Sash-Reek2010/The-Mech/PCB/KiCAD/KEEB.kicad_sch

## KiCad design PCB/KiCAD/KEEB.kicad_sch (2026-04-22)

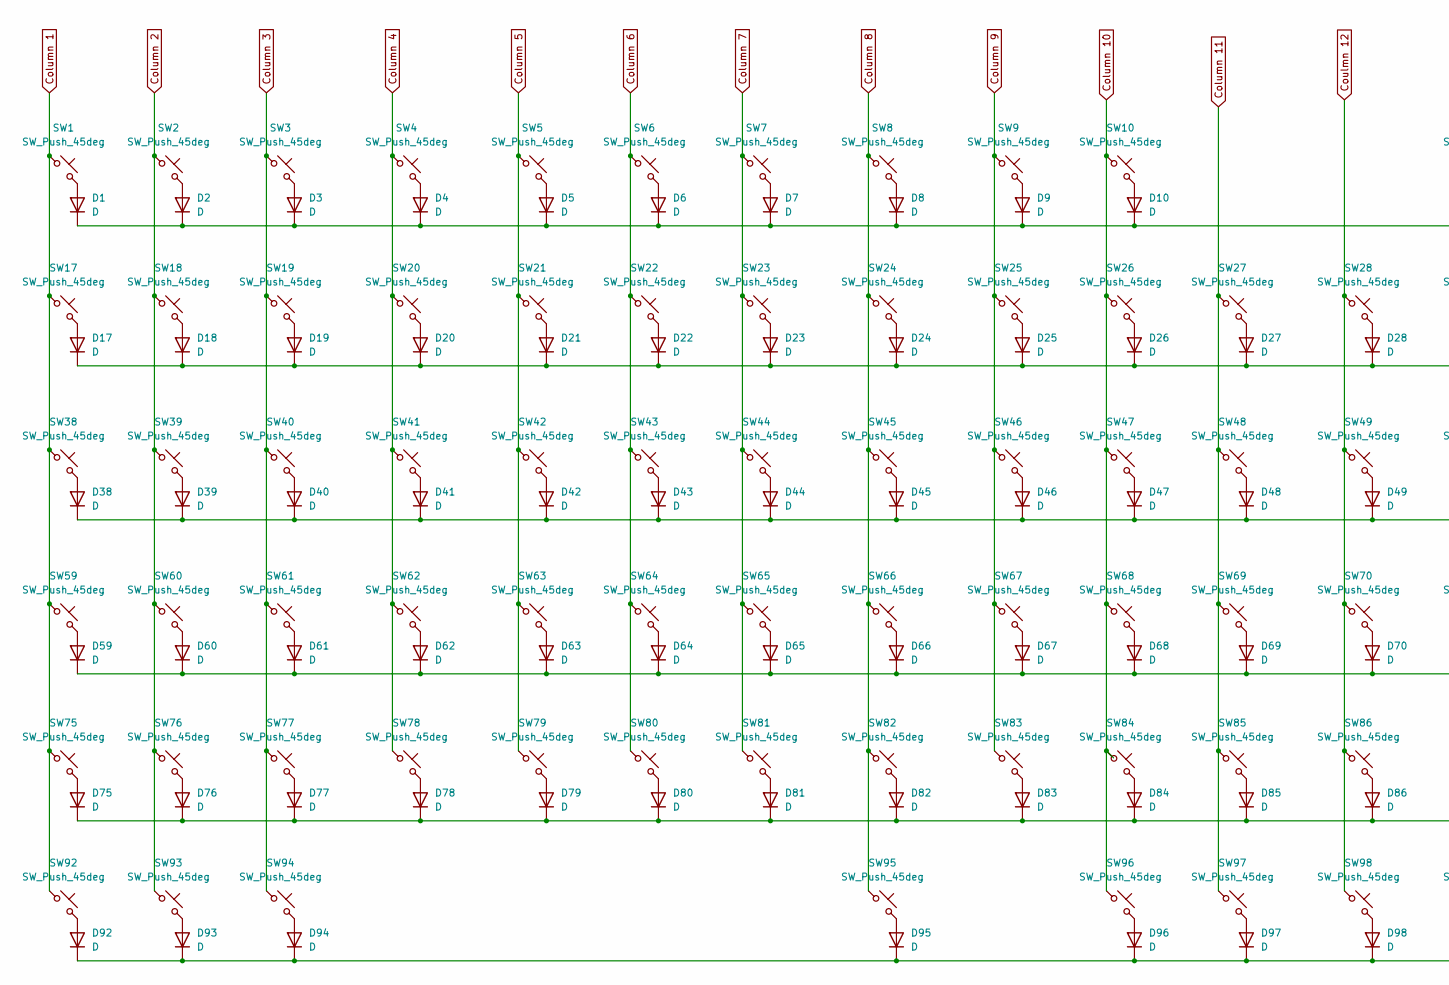
[picture p3: schematic KEEB.kicad_sch, part in row 1, column 1]

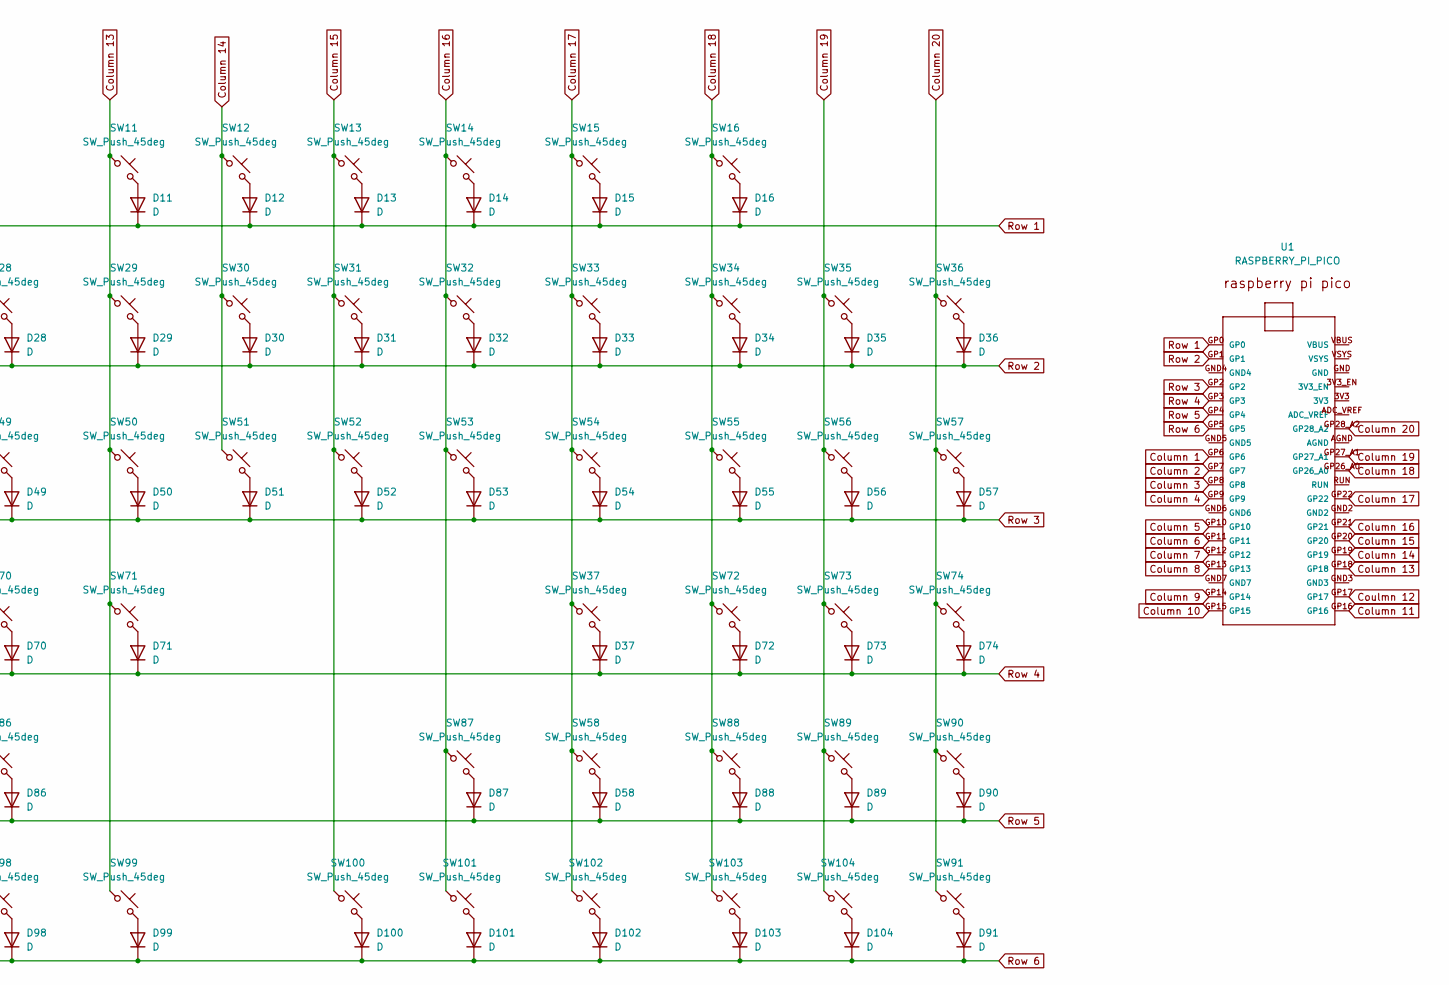
[picture p4: schematic KEEB.kicad_sch, part in row 1, column 2]

Parts:
D1, D2, D3, D4, D5, D6, D7, D8, D9, D10, D11, D12, D13, D14, D15, D16, D17, D18, D19, D20, D21, D22, D23, D24, D25, D26, D27, D28, D29, D30, D31, D32, D33, D34, D35, D36, D37, D38, D39, D40, D41, D42, D43, D44, D45, D46, D47, D48, D49, D50, D51, D52, D53, D54, D55, D56, D57, D58, D59, D60, D61, D62, D63, D64, D65, D66, D67, D68, D69, D70, D71, D72, D73, D74, D75, D76, D77, D78, D79, D80, D81, D82, D83, D84, D85, D86, D87, D88, D89, D90, D91, D92, D93, D94, D95, D96, D97, D98, D99, D100, D101, D102, D103, D104: D; Diode_DO-35
SW1, SW2, SW3, SW4, SW5, SW6, SW7, SW8, SW9, SW10, SW11, SW12, SW13, SW14, SW15, SW16, SW17, SW18, SW19, SW20, SW21, SW22, SW23, SW24, SW25, SW26, SW27, SW28, SW29, SW31, SW32, SW33, SW34, SW35, SW36, SW37, SW39, SW40, SW41, SW42, SW43, SW44, SW45, SW46, SW47, SW48, SW49, SW50, SW52, SW53, SW54, SW55, SW56, SW57, SW60, SW61, SW62, SW63, SW64, SW65, SW66, SW67, SW68, SW69, SW70, SW72, SW73, SW74, SW76, SW77, SW78, SW79, SW80, SW81, SW82, SW83, SW84, SW85, SW87, SW88, SW89, SW90, SW100, SW101, SW102, SW104: SW_Push_45deg; MX_PCB_1.00u
SW30, SW103: SW_Push_45deg; CherryMX_2.00u_StabWireTop
SW38, SW51: SW_Push_45deg; MX_PCB_1.50u
SW58, SW91: SW_Push_45deg; CherryMX_2.00u_PCB_StabWireTop TRUE ROTATED
SW59: SW_Push_45deg; MX_PCB_1.75u
SW71, SW75: SW_Push_45deg; CherryMX_2.25u_StabWireTop
SW86: SW_Push_45deg; CherryMX_2.75u_StabWireTop
SW92, SW93, SW94, SW96, SW97, SW98, SW99: SW_Push_45deg; MX_PCB_1.25u
SW95: SW_Push_45deg; CherryMX_6.25u_StabWireTop
U1: RASPBERRY_PI_PICO

Connections:
Column 1: SW1.1, SW17.1, SW38.1, SW59.1, SW75.1, SW92.1, U1.GP6
Column 2: SW2.1, SW18.1, SW39.1, SW60.1, SW76.1, SW93.1, U1.GP7
Column 3: SW3.1, SW19.1, SW40.1, SW61.1, SW77.1, SW94.1, U1.GP8
Column 4: SW4.1, SW20.1, SW41.1, SW62.1, SW78.1, U1.GP9
Column 5: SW5.1, SW21.1, SW42.1, SW63.1, SW79.1, U1.GP10
Column 6: SW6.1, SW22.1, SW43.1, SW64.1, SW80.1, U1.GP11
Column 7: SW7.1, SW23.1, SW44.1, SW65.1, SW81.1, U1.GP12
Column 8: SW8.1, SW24.1, SW45.1, SW66.1, SW82.1, SW95.1, U1.GP13
Column 9: SW9.1, SW25.1, SW46.1, SW67.1, SW83.1, U1.GP14
Column 10: SW10.1, SW26.1, SW47.1, SW68.1, SW84.1, SW96.1, U1.GP15
Column 11: SW27.1, SW48.1, SW69.1, SW85.1, SW97.1, U1.GP16
Column 13: SW11.1, SW29.1, SW50.1, SW71.1, SW99.1, U1.GP18
Column 14: SW12.1, SW30.1, SW51.1, U1.GP19
Column 15: SW13.1, SW31.1, SW52.1, SW100.1, U1.GP20
Column 16: SW14.1, SW32.1, SW53.1, SW87.1, SW101.1, U1.GP21
Column 17: SW15.1, SW33.1, SW37.1, SW54.1, SW58.1, SW102.1, U1.GP22
Column 18: SW16.1, SW34.1, SW55.1, SW72.1, SW88.1, SW103.1, U1.GP26_A0
Column 19: SW35.1, SW56.1, SW73.1, SW89.1, SW104.1, U1.GP27_A1
Column 20: SW36.1, SW57.1, SW74.1, SW90.1, SW91.1, U1.GP28_A2
Coulmn 12: SW28.1, SW49.1, SW70.1, SW86.1, SW98.1, U1.GP17
unnamed: D1.2 (A), SW1.2
unnamed: D2.2 (A), SW2.2
unnamed: D3.2 (A), SW3.2
unnamed: D4.2 (A), SW4.2
unnamed: D5.2 (A), SW5.2
unnamed: D6.2 (A), SW6.2
unnamed: D7.2 (A), SW7.2
unnamed: D8.2 (A), SW8.2
unnamed: D9.2 (A), SW9.2
unnamed: D10.2 (A), SW10.2
unnamed: D11.2 (A), SW11.2
unnamed: D12.2 (A), SW12.2
unnamed: D13.2 (A), SW13.2
unnamed: D14.2 (A), SW14.2
unnamed: D15.2 (A), SW15.2
unnamed: D16.2 (A), SW16.2
unnamed: D17.2 (A), SW17.2
unnamed: D18.2 (A), SW18.2
unnamed: D19.2 (A), SW19.2
unnamed: D20.2 (A), SW20.2
unnamed: D21.2 (A), SW21.2
unnamed: D22.2 (A), SW22.2
unnamed: D23.2 (A), SW23.2
unnamed: D24.2 (A), SW24.2
unnamed: D25.2 (A), SW25.2
unnamed: D26.2 (A), SW26.2
unnamed: D27.2 (A), SW27.2
unnamed: D28.2 (A), SW28.2
unnamed: D29.2 (A), SW29.2
unnamed: D30.2 (A), SW30.2
unnamed: D31.2 (A), SW31.2
unnamed: D32.2 (A), SW32.2
unnamed: D33.2 (A), SW33.2
unnamed: D34.2 (A), SW34.2
unnamed: D35.2 (A), SW35.2
unnamed: D36.2 (A), SW36.2
unnamed: D37.2 (A), SW37.2
unnamed: D38.2 (A), SW38.2
unnamed: D39.2 (A), SW39.2
unnamed: D40.2 (A), SW40.2
unnamed: D41.2 (A), SW41.2
unnamed: D42.2 (A), SW42.2
unnamed: D43.2 (A), SW43.2
unnamed: D44.2 (A), SW44.2
unnamed: D45.2 (A), SW45.2
unnamed: D46.2 (A), SW46.2
unnamed: D47.2 (A), SW47.2
unnamed: D48.2 (A), SW48.2
unnamed: D49.2 (A), SW49.2
unnamed: D50.2 (A), SW50.2
unnamed: D51.2 (A), SW51.2
unnamed: D52.2 (A), SW52.2
unnamed: D53.2 (A), SW53.2
unnamed: D54.2 (A), SW54.2
unnamed: D55.2 (A), SW55.2
unnamed: D56.2 (A), SW56.2
unnamed: D57.2 (A), SW57.2
unnamed: D58.2 (A), SW58.2
unnamed: D59.2 (A), SW59.2
unnamed: D60.2 (A), SW60.2
unnamed: D61.2 (A), SW61.2
unnamed: D62.2 (A), SW62.2
unnamed: D63.2 (A), SW63.2
unnamed: D64.2 (A), SW64.2
unnamed: D65.2 (A), SW65.2
unnamed: D66.2 (A), SW66.2
unnamed: D67.2 (A), SW67.2
unnamed: D68.2 (A), SW68.2
unnamed: D69.2 (A), SW69.2
unnamed: D70.2 (A), SW70.2
unnamed: D71.2 (A), SW71.2
unnamed: D72.2 (A), SW72.2
unnamed: D73.2 (A), SW73.2
unnamed: D74.2 (A), SW74.2
unnamed: D75.2 (A), SW75.2
unnamed: D76.2 (A), SW76.2
unnamed: D77.2 (A), SW77.2
unnamed: D78.2 (A), SW78.2
unnamed: D79.2 (A), SW79.2
unnamed: D80.2 (A), SW80.2
unnamed: D81.2 (A), SW81.2
unnamed: D82.2 (A), SW82.2
unnamed: D83.2 (A), SW83.2
unnamed: D84.2 (A), SW84.2
unnamed: D85.2 (A), SW85.2
unnamed: D86.2 (A), SW86.2
unnamed: D87.2 (A), SW87.2
unnamed: D88.2 (A), SW88.2
unnamed: D89.2 (A), SW89.2
unnamed: D90.2 (A), SW90.2
unnamed: D91.2 (A), SW91.2
unnamed: D92.2 (A), SW92.2
unnamed: D93.2 (A), SW93.2
unnamed: D94.2 (A), SW94.2
unnamed: D95.2 (A), SW95.2
unnamed: D96.2 (A), SW96.2
unnamed: D97.2 (A), SW97.2
unnamed: D98.2 (A), SW98.2
unnamed: D99.2 (A), SW99.2
unnamed: D100.2 (A), SW100.2
unnamed: D101.2 (A), SW101.2
unnamed: D102.2 (A), SW102.2
unnamed: D103.2 (A), SW103.2
unnamed: D104.2 (A), SW104.2
Row 1: D1.1 (K), D2.1 (K), D3.1 (K), D4.1 (K), D5.1 (K), D6.1 (K), D7.1 (K), D8.1 (K), D9.1 (K), D10.1 (K), D11.1 (K), D12.1 (K), D13.1 (K), D14.1 (K), D15.1 (K), D16.1 (K), U1.GP0
Row 2: D17.1 (K), D18.1 (K), D19.1 (K), D20.1 (K), D21.1 (K), D22.1 (K), D23.1 (K), D24.1 (K), D25.1 (K), D26.1 (K), D27.1 (K), D28.1 (K), D29.1 (K), D30.1 (K), D31.1 (K), D32.1 (K), D33.1 (K), D34.1 (K), D35.1 (K), D36.1 (K), U1.GP1
Row 3: D38.1 (K), D39.1 (K), D40.1 (K), D41.1 (K), D42.1 (K), D43.1 (K), D44.1 (K), D45.1 (K), D46.1 (K), D47.1 (K), D48.1 (K), D49.1 (K), D50.1 (K), D51.1 (K), D52.1 (K), D53.1 (K), D54.1 (K), D55.1 (K), D56.1 (K), D57.1 (K), U1.GP2
Row 4: D37.1 (K), D59.1 (K), D60.1 (K), D61.1 (K), D62.1 (K), D63.1 (K), D64.1 (K), D65.1 (K), D66.1 (K), D67.1 (K), D68.1 (K), D69.1 (K), D70.1 (K), D71.1 (K), D72.1 (K), D73.1 (K), D74.1 (K), U1.GP3
Row 5: D58.1 (K), D75.1 (K), D76.1 (K), D77.1 (K), D78.1 (K), D79.1 (K), D80.1 (K), D81.1 (K), D82.1 (K), D83.1 (K), D84.1 (K), D85.1 (K), D86.1 (K), D87.1 (K), D88.1 (K), D89.1 (K), D90.1 (K), U1.GP4
Row 6: D91.1 (K), D92.1 (K), D93.1 (K), D94.1 (K), D95.1 (K), D96.1 (K), D97.1 (K), D98.1 (K), D99.1 (K), D100.1 (K), D101.1 (K), D102.1 (K), D103.1 (K), D104.1 (K), U1.GP5
